kodachi614/macropaw/Beatboxer/renders/Bottom (raytraced).png

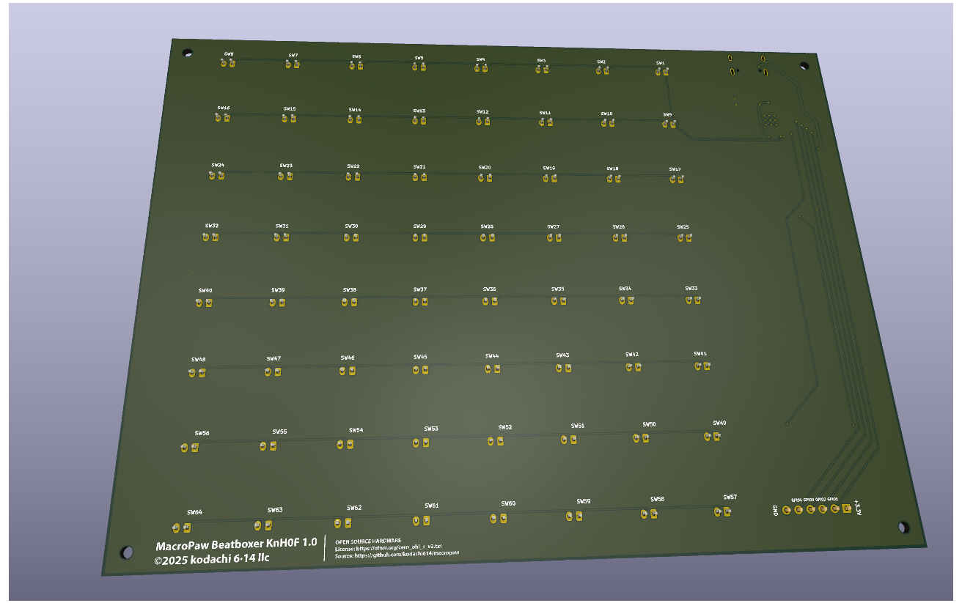
Beatboxer/renders/Bottom (raytraced).png
