kodachi614/macropaw/photos/KnGXT-board-bottom.png

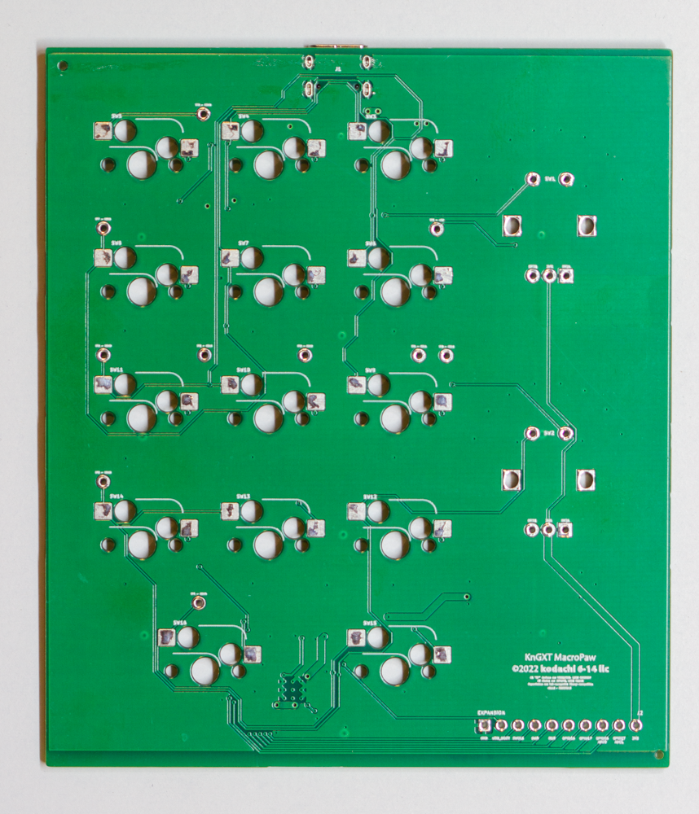
photos/KnGXT-board-bottom.png
